introlab/OpenIMU-MiniLogger/Firmware-Arduino/src/imu.cpp

#include "imu.h"
#include "configmanager.h"
#include "sdcard.h"

IMU* IMU::_instance = NULL;

namespace
{
    /**
     * Interrupt handler will wake up the readIMU task at every sample (for each axis). 
     */
    void IRAM_ATTR imu_gpio_isr_handler(void* arg)
    {
        IMU *imu = (IMU*) (arg);
        assert(imu != NULL);
        xSemaphoreGiveFromISR(imu->getSemaphore(), NULL);
    }


    void readIMU(void *pvParameters)
    {
        printf("readIMU starting \n");
        IMU *imu = (IMU*) (pvParameters);
        assert(imu != NULL);

        TickType_t lastPrint = xTaskGetTickCount();
        TickType_t now;

        while(1)
        {
            xSemaphoreTake(imu->getSemaphore(), portMAX_DELAY);
            //printf("should read from task\n");
            imuDataPtr_t data = (imuDataPtr_t) malloc(sizeof(imuData_t));
            imu->readSensor(data);

            //Print at 4 Hz for debug
            /*
            now = xTaskGetTickCount();
            if (now - lastPrint > 250 / portTICK_RATE_MS)
            {
                printf("\nAccel : %.2f\t%.2f\t%.2f\n", data->accelX, data->accelY, data->accelZ);
                printf("Mag   : %.2f\t%.2f\t%.2f\n", data->magX, data->magY, data->magZ);
                printf("Gyro  : %.2f\t%.2f\t%.2f\n", data->gyroX, data->gyroY, data->gyroZ);
                lastPrint = now;
            }
            */

            //Send to queue, delete if not working
            if (!SDCard::instance()->enqueue(data))
                free(data);


        }
    }

}



IMU::IMU()
    : _mpu9250(), _readIMUHandle(NULL)
{
    if (_mpu9250.begin() == 0)
    {
        //IMUconfig_Sd SdConfig={100,500,8};

        setIMUParameter(ConfigManager::instance()->getIMUConfig());
               
        //SDCard::instance()->GetConfigFromSd(&SdConfig);
        //setIMUParameter(SdConfig.IMUSampleRate,SdConfig.IMUAcellRange,SdConfig.IMUGyroRange);

        printf("initialisation\n");


        // Enable FIFO
        //_mpu9250.enableFifo(true, true, true, true);

        
        // Setup interrupt handling
        _semaphore = xSemaphoreCreateCounting(1,0);
        setup_interrupt_pin();
        _mpu9250.enableInterrupt();
        _mpu9250.setIntLevel(INT_ACTIVE_LOW);

        //Create reading task, maximum priority
        xTaskCreatePinnedToCore(&readIMU, "IMU read task", 2048, this, configMAX_PRIORITIES -1, &_readIMUHandle, 0);
        //xTaskCreate(&readIMU, "IMU read task", 2048, this, 10, &_readIMUHandle);
        printf("IMU initialized\n");
    }
    else
    {
        printf("ERROR initializing IMU\n");
    }
}

void IMU::readSensor(imuDataPtr_t data)
{
    _mpu9250.update();

    if (data)
    {
        data->accelX = _mpu9250.calcAccel(_mpu9250.ax);
        data->accelY = _mpu9250.calcAccel(_mpu9250.ay);
        data->accelZ = _mpu9250.calcAccel(_mpu9250.az);
        data->gyroX  = _mpu9250.calcGyro(_mpu9250.gx);
        data->gyroY  = _mpu9250.calcGyro(_mpu9250.gy);
        data->gyroZ  = _mpu9250.calcGyro(_mpu9250.gz);
        data->magX = _mpu9250.calcMag(_mpu9250.mx);
        data->magY = _mpu9250.calcMag(_mpu9250.my);
        data->magZ = _mpu9250.calcMag(_mpu9250.mz);

    }
}

IMU* IMU::instance()
{
    if (IMU::_instance == NULL)
        IMU::_instance = new IMU();
    return IMU::_instance;
}

void IMU::setup_interrupt_pin()
{
    gpio_config_t io_conf;
    //interrupt on falling edge
    io_conf.intr_type = (gpio_int_type_t) GPIO_PIN_INTR_NEGEDGE;
    //set as input mode
    io_conf.mode = GPIO_MODE_INPUT;
    //bit mask of the pins that you want to set,e.g.GPIO33
    io_conf.pin_bit_mask =  (1ULL << INTERRUPT_PIN);
    //disable pull-down mode
    io_conf.pull_down_en = (gpio_pulldown_t) 0;
    //enable pull-up mode
    io_conf.pull_up_en = (gpio_pullup_t) 1;
    //configure GPIO with the given settings
    gpio_config(&io_conf);


    //Set ISR
    gpio_isr_handler_add((gpio_num_t)INTERRUPT_PIN, imu_gpio_isr_handler, this);
}

void IMU::setSampleRate(int rateHz)
{
    if (rateHz==10)
    {
        //_mpu9250.setDlpfBandwidth(DLPF_BANDWIDTH_5HZ);
        _mpu9250.setSampleRate(10);
        _mpu9250.setCompassSampleRate(10);

        printf("Set sample Rate:10Hz\n");
        SampleRateHz=10;
    }
    else if (rateHz==50)
    {
        //_mpu9250.setDlpfBandwidth(DLPF_BANDWIDTH_5HZ);
        _mpu9250.setSampleRate(50);
        _mpu9250.setCompassSampleRate(50);
        
        printf("Set sample Rate:50Hz\n");

        SampleRateHz=50;
    }
    else if (rateHz==100)
    {
        //_mpu9250.setLPF(42);
        _mpu9250.setSampleRate(100);
        _mpu9250.setCompassSampleRate(100);
        
        printf("Set sample Rate:100Hz\n");

        SampleRateHz=100;
    }
    else if (rateHz==200)
    {
        //_mpu9250.setLPF(98);
        _mpu9250.setSampleRate(200);
        _mpu9250.setCompassSampleRate(100);
        
        printf("Set sample Rate:200Hz\n");

        SampleRateHz=200;
    }
    else
    {
        _mpu9250.setSampleRate(100);
        _mpu9250.setCompassSampleRate(100);
        printf("Wrong rate entered,setting to 100Hz");

        SampleRateHz=100;
    }
    
}

void IMU::setGyroRange(int Gyrorange)
{
    if (Gyrorange==250 || Gyrorange == 500 || Gyrorange == 1000 || Gyrorange == 2000)
    {
        _mpu9250.setGyroFSR(Gyrorange);
        printf("Set Gyroscope range: %d\n",Gyrorange);
        GyroRangeDPS=Gyrorange;
    }
    else 
    {
        printf("Wrong range entered, setting to 500 dps\n");
        _mpu9250.setGyroFSR(500);
    }
}

void IMU::setAccelRange(int Accelrange)
{
    if (Accelrange==2 || Accelrange == 4 || Accelrange == 8 || Accelrange == 16)
    {
        _mpu9250.setAccelFSR(Accelrange);
        printf("Set Accelerometer range: %d\n",Accelrange);
        AccelRangeG=Accelrange;
    }
    else 
    {
        printf("Wrong range entered, setting to 4 g\n");
        _mpu9250.setAccelFSR(4);
    }
}

void IMU::setIMUParameter(int rateHZ,int accelRange, int gyroRange)
{
    // The sample rate of the accel/gyro can be set using
    // setSampleRate. Acceptable values range from 4Hz to 1kHz

    setSampleRate(rateHZ);

    // Accel options are +/- 2, 4, 8, or 16 g
    setAccelRange(accelRange);
    
    // Use setGyroFSR() and setAccelFSR() to configure the
    // gyroscope and accelerometer full scale ranges.
    // Gyro options are +/- 250, 500, 1000, or 2000 dps
    setGyroRange(gyroRange);
  
}

void IMU::setIMUParameter(const IMUconfig_Sd &config)
{
    setIMUParameter(config.IMUSampleRate, config.IMUAcellRange, config.IMUGyroRange);
}

int IMU::getSampleRate()
{
    int id = 0;
    if (SampleRateHz==10)
        id = 1;
    else if (SampleRateHz==50)
        id = 2;
    else if (SampleRateHz==100)
        id = 3;
    else if (SampleRateHz==200)
        id = 4;

    return id;
}

int IMU::getGyroRange()
{
    int id = 0;
    if (GyroRangeDPS==250)
        id = 1;
    else if (GyroRangeDPS==500)
        id = 2;
    else if (GyroRangeDPS==1000)
        id = 3;
    else if (GyroRangeDPS==2000)
        id = 4;

    return id;
}

int IMU::getAccelRange()
{
    int id = 0;
    if (AccelRangeG==2)
        id = 1;
    else if (AccelRangeG==4)
        id = 2;
    else if (AccelRangeG==8)
        id = 3;
    else if (AccelRangeG==16)
        id = 4;

    return id;
}


int IMU::getStepCount()
{
    return _mpu9250.dmpGetPedometerSteps();
}
    
int IMU::getStepTime()
{
    return _mpu9250.dmpGetPedometerTime()/1000;
}
