introlab/OpenIMU-MiniLogger/Firmware-Arduino/src/widget/icons.h

/*
 * Homescreen icons for Open Imu
 * 
 * Export as 1bpp in GIMP
 * Convert with https://littlevgl.com/image-to-c-array
 * 
 * author: Cedric Godin
 * 
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
 * THE SOFTWARE IS PROVIDED "AS IS", WITHOUT WARRANTY OF ANY KIND, EXPRESS OR IMPLIED, INCLUDING BUT NOT
 * LIMITED TO THE WARRANTIES OF MERCHANTABILITY, FITNESS FOR A PARTICULAR PURPOSE AND NONINFRINGEMENT.
 * IN NO EVENT SHALL THE AUTHORS OR COPYRIGHT HOLDERS BE LIABLE FOR ANY CLAIM, DAMAGES OR OTHER LIABILITY,
 * WHETHER IN AN ACTION OF CONTRACT, TORT OR OTHERWISE, ARISING FROM, OUT OF OR IN CONNECTION WITH THE SOFTWARE
 * OR THE USE OR OTHER DEALINGS IN THE SOFTWARE.
 */

#pragma once

#define GPS_ICON_WIDTH 13
#define GPS_ICON_HEIGHT 26

const unsigned char gps_icon[] = {
  0x0f, 0x80, 
  0x30, 0x60, 
  0x60, 0x30, 
  0x4f, 0x90, 
  0x90, 0x48, 
  0x90, 0x48, 
  0x90, 0x48, 
  0x90, 0x48, 
  0x90, 0x48, 
  0x4d, 0x90, 
  0x42, 0x10, 
  0x40, 0x10, 
  0x20, 0x10, 
  0x20, 0x20, 
  0x30, 0x20, 
  0x10, 0x40, 
  0x10, 0x40, 
  0x08, 0x80, 
  0x0c, 0x80, 
  0x05, 0x80, 
  0x37, 0x60, 
  0x43, 0x10, 
  0x82, 0x08, 
  0x80, 0x08, 
  0x60, 0x30, 
  0x1f, 0xc0
};

#define BATTERY_ICON_WIDTH 10
#define BATTERY_ICON_HEIGHT 25

const unsigned char battery_icon[] = {
  0x3f, 0x00, 
  0x21, 0x00, 
  0xff, 0xc0, 
  0x80, 0x40, 
  0x80, 0x40, 
  0x80, 0x40, 
  0x80, 0x40, 
  0x80, 0x40, 
  0x80, 0x40, 
  0x80, 0x40, 
  0x80, 0x40, 
  0x80, 0x40, 
  0x80, 0x40, 
  0x80, 0x40, 
  0x80, 0x40, 
  0x80, 0x40, 
  0x80, 0x40, 
  0x80, 0x40, 
  0x80, 0x40, 
  0x80, 0x40, 
  0x80, 0x40, 
  0x80, 0x40, 
  0x80, 0x40, 
  0x80, 0x40, 
  0xff, 0xc0
};

#define LOGGING_ICON_WIDTH 18
#define LOGGING_ICON_HEIGHT 21

const unsigned char logging_icon[] {
  0x00, 0x70, 0x00, 
  0x00, 0x50, 0x00, 
  0x00, 0x50, 0x00, 
  0x00, 0x50, 0x00, 
  0x01, 0xdc, 0x00, 
  0x01, 0x04, 0x00, 
  0x00, 0x88, 0x00, 
  0x00, 0x88, 0x00, 
  0x00, 0x50, 0x00, 
  0x1f, 0x77, 0xc0, 
  0x10, 0x20, 0x40, 
  0xff, 0xfe, 0x40, 
  0x80, 0x01, 0x40, 
  0x80, 0x01, 0x40, 
  0x40, 0x01, 0x40, 
  0x40, 0x01, 0xc0, 
  0x40, 0x00, 0xc0, 
  0x20, 0x00, 0xc0, 
  0x20, 0x00, 0xc0, 
  0x20, 0x00, 0x40, 
  0x3f, 0xff, 0xc0
};

#define SD_ICON_WIDTH 18
#define SD_ICON_HEIGHT 24

const unsigned char sd_icon[] {
  0x0f, 0xff, 0xc0, 
  0x10, 0x00, 0x40, 
  0x10, 0x00, 0x40, 
  0x20, 0x00, 0x40, 
  0x40, 0x00, 0x40, 
  0xc0, 0x00, 0x40, 
  0x80, 0x00, 0x40, 
  0x80, 0x00, 0x40, 
  0x80, 0x00, 0x40, 
  0x80, 0x00, 0x40, 
  0x80, 0x00, 0x40, 
  0x80, 0x00, 0x40, 
  0x9e, 0x78, 0x40, 
  0xb1, 0x46, 0x40, 
  0xa0, 0x43, 0x40, 
  0xa0, 0x41, 0x40, 
  0x9e, 0x41, 0x40, 
  0x83, 0x41, 0x40, 
  0x81, 0x41, 0x40, 
  0x81, 0x42, 0x40, 
  0xbe, 0x7c, 0x40, 
  0x80, 0x00, 0x40, 
  0x80, 0x00, 0x40, 
  0xff, 0xff, 0xc0
};

#define USB_ICON_WIDTH 15
#define USB_ICON_HEIGHT 25

const unsigned char usb_icon[] {
  0x01, 0x00, 
  0x01, 0x00, 
  0x03, 0x80, 
  0x03, 0x80, 
  0x07, 0xc0, 
  0x01, 0x00, 
  0x01, 0x00, 
  0x01, 0x1e, 
  0x01, 0x1e, 
  0x61, 0x1e, 
  0xf1, 0x1e, 
  0xf1, 0x04, 
  0x61, 0x0c, 
  0x41, 0x18, 
  0x61, 0xf0, 
  0x31, 0x00, 
  0x1d, 0x00, 
  0x03, 0x00, 
  0x01, 0x00, 
  0x01, 0x00, 
  0x03, 0x80, 
  0x07, 0xc0, 
  0x07, 0xc0, 
  0x07, 0xc0, 
  0x03, 0x80
};

#define SAMPLERATE_ICON_WIDTH 20
#define SAMPLERATE_ICON_HEIGHT 25

const unsigned char samplerate_icon[] = {
 0x00,0x00,0xf0,0x00,0x00,0xf0,0x06,0xfb,0xf7,0x06,0xfb,0xf7,
 0x06,0x03,0xf6,0x06,0x03,0xf6,0x06,0x03,0xf7,0x06,0x83,0xf3,
 0x06,0x83,0xf1,0x06,0x83,0xf1,0x06,0x83,0xf1,0xfe,0xc3,0xf0,
 0xfe,0xc3,0xf0,0x06,0xe3,0xf0,0x06,0x63,0xf0,0x06,0x63,0xf0,
 0x06,0x33,0xf0,0x06,0x3b,0xf0,0x06,0x1b,0xf0,0x06,0x1b,0xf0,
 0x06,0xfb,0xf7,0x06,0xfb,0xf7,0x00,0x00,0xf0,0x00,0x00,0xf0,
 0x00,0x00,0xf0};
