introlab/OpenIMU-MiniLogger/tests/OLED-Test-Firmware/include/ssd1331.h

/*****************************************************************************
*
* File                : ssd1331.h
* Hardware Environment: Raspberry Pi
* Build Environment   : GCC
* Version             : V1.0.7
* Author              : Yehui
*
*              (c) Copyright 2005-2017, WaveShare
*                   http://www.waveshare.com
*                   http://www.waveshare.net   
*                      All Rights Reserved
*              
******************************************************************************/

#ifndef _SSD1331_H_
#define _SSD1331_H_

//Display defines
#define OLED_WIDTH 96
#define OLED_HEIGHT 64

#define RGB(R,G,B)  (((R >> 3) << 11) | ((G >> 2) << 5) | (B >> 3))
enum Color {
    BLACK     = RGB(  0,  0,  0), // black
    GRAY      = RGB(192,192,192), // gray
    WHITE     = RGB(255,255,255), // white
    RED       = RGB(255,  0,  0), // red
    PINK      = RGB(255,192,203), // pink
    YELLOW    = RGB(255,255,  0), // yellow
    GOLDEN    = RGB(255,215,  0), // golden
    BROWN     = RGB(128, 42, 42), // brown
    BLUE      = RGB(  0,  0,255), // blue
    CYAN      = RGB(  0,255,255), // cyan
    GREEN     = RGB(  0,255,  0), // green
    PURPLE    = RGB(160, 32,240), // purple
};

enum ColorCMD {
    BLACK_CMD,
    GRAY_CMD,
    WHITE_CMD,
    RED_CMD,
    PINK_CMD,
    YELLOW_CMD,
    GOLDEN_CMD,
    BROWN_CMD,
    BLUE_CMD,
    CYAN_CMD,
    GREEN_CMD,
    PURPLE_CMD,
};

static const unsigned char color_cmd[12][3] =  {
    {0, 0, 0},
    {192, 192, 192},
    {255, 255, 255},
    {255,  0,  0},
    {255,192,203},
    {255,255,  0},
    {255,215,  0},
    {128, 42, 42},
    {  0,  0,255},
    {  0,255,255},
    {  0,255,  0},
    {160, 32,240},
};

#define DRAW_LINE                       0x21
#define DRAW_RECTANGLE                  0x22
#define COPY_WINDOW                     0x23
#define DIM_WINDOW                      0x24
#define CLEAR_WINDOW                    0x25
#define FILL_WINDOW                     0x26
#define DISABLE_FILL                    0x00
#define ENABLE_FILL                     0x01
#define CONTINUOUS_SCROLLING_SETUP      0x27
#define DEACTIVE_SCROLLING              0x2E
#define ACTIVE_SCROLLING                0x2F

#define SET_COLUMN_ADDRESS              0x15
#define SET_ROW_ADDRESS                 0x75
#define SET_CONTRAST_A                  0x81
#define SET_CONTRAST_B                  0x82
#define SET_CONTRAST_C                  0x83
#define MASTER_CURRENT_CONTROL          0x87
#define SET_PRECHARGE_SPEED_A           0x8A
#define SET_PRECHARGE_SPEED_B           0x8B
#define SET_PRECHARGE_SPEED_C           0x8C
#define SET_REMAP                       0xA0
#define SET_DISPLAY_START_LINE          0xA1
#define SET_DISPLAY_OFFSET              0xA2
#define NORMAL_DISPLAY                  0xA4
#define ENTIRE_DISPLAY_ON               0xA5
#define ENTIRE_DISPLAY_OFF              0xA6
#define INVERSE_DISPLAY                 0xA7
#define SET_MULTIPLEX_RATIO             0xA8
#define DIM_MODE_SETTING                0xAB
#define SET_MASTER_CONFIGURE            0xAD
#define DIM_MODE_DISPLAY_ON             0xAC
#define DISPLAY_OFF                     0xAE
#define NORMAL_BRIGHTNESS_DISPLAY_ON    0xAF
#define POWER_SAVE_MODE                 0xB0
#define PHASE_PERIOD_ADJUSTMENT         0xB1
#define DISPLAY_CLOCK_DIV               0xB3
#define SET_GRAy_SCALE_TABLE            0xB8
#define ENABLE_LINEAR_GRAY_SCALE_TABLE  0xB9
#define SET_PRECHARGE_VOLTAGE           0xBB

#define SET_V_VOLTAGE                   0xBE

void SSD1331_begin();
void SSD1331_display();
void SSD1331_clear();
void SSD1331_shutdown();
void SSD1331_pixel(int x,int y, char color);
void SSD1331_rectangle(int x1, int y1, int x2, int y2, unsigned short hwColor, bool filled = false);
void SSD1331_line(int x1, int y1, int x2, int y2, unsigned short hwColor);
void SSD1331_mono_bitmap(unsigned char x, unsigned char y, const unsigned char *pBmp, char chWidth, char chHeight, unsigned short hwColor);
void SSD1331_bitmap24(unsigned char x, unsigned char y, unsigned char *pBmp, char chWidth, char chHeight);
void SSD1331_string(unsigned char x, unsigned char y, const char *pString, unsigned char Size, unsigned char Mode, unsigned short hwColor);
void SSD1331_char1616(unsigned char x, unsigned char y, unsigned char chChar, unsigned short hwColor);
void SSD1331_char3216(unsigned char x, unsigned char y, unsigned char chChar, unsigned short hwColor);

void SSD1331_clear_screen(unsigned short hwColor);
void SSD1331_draw_point(int chXpos, int chYpos, unsigned short hwColor);

static const unsigned char waveshare_logo[1024]=
{/*0X00,0X01,0X60,0X00,0X40,0X00,*/
    0X00,0X00,0X00,0X00,0X00,0X00,0X00,0X00,0X00,0X00,0X00,0X00,0X00,0X00,0X00,0X00,
    0X00,0X00,0X00,0X00,0X00,0X00,0X00,0X00,0X00,0X00,0X00,0X00,0X00,0X00,0X00,0X00,
    0X00,0X00,0X00,0X00,0X00,0X00,0X00,0X00,0X00,0X00,0X00,0X00,0X00,0X00,0X00,0X00,
    0X41,0X83,0X0C,0X30,0X33,0XF1,0XF8,0XC1,0X81,0X81,0XFC,0X7E,0X61,0XC2,0X0E,0X10,
    0X33,0X03,0X00,0XC1,0X83,0X81,0X8C,0X60,0X61,0XC2,0X1A,0X18,0X23,0X03,0X00,0XC1,
    0X82,0XC1,0X84,0X60,0X63,0X46,0X12,0X18,0X63,0X03,0X00,0XC1,0X82,0X41,0X84,0X60,
    0X23,0X46,0X33,0X08,0X43,0X01,0X80,0XC1,0X86,0X61,0X8C,0X60,0X32,0X64,0X31,0X0C,
    0XC3,0XF0,0XE0,0XFF,0X84,0X61,0XF8,0X7E,0X32,0X64,0X21,0X8C,0XC3,0X00,0X30,0XC1,
    0X8C,0X21,0XF0,0X60,0X16,0X2C,0X7F,0X84,0X83,0X00,0X18,0XC1,0X8F,0XF1,0X98,0X60,
    0X1C,0X3C,0X7F,0X87,0X83,0X00,0X18,0XC1,0X8F,0XF1,0X8C,0X60,0X1C,0X38,0XC0,0XC7,
    0X83,0X02,0X18,0XC1,0X98,0X11,0X86,0X60,0X0C,0X18,0XC0,0XC3,0X03,0XF3,0XF0,0XC1,
    0X98,0X19,0X86,0X7E,0X08,0X18,0X80,0X43,0X03,0XF0,0XE0,0XC1,0X90,0X09,0X02,0X7E,
    0X00,0X00,0X00,0X00,0X00,0X00,0X00,0X00,0X00,0X00,0X00,0X00,0X00,0X00,0X00,0X00,
    0X00,0X00,0X00,0X00,0X00,0X00,0X00,0X00,0X00,0X00,0X00,0X00,0X00,0X00,0X00,0X00,
    0X00,0X00,0X00,0X00,0X00,0X00,0X00,0X00,0X00,0X00,0X00,0X00,0X00,0X00,0X00,0X00,
    0X00,0X00,0X00,0X00,0X00,0X00,0X00,0X00,0X00,0X00,0X00,0X00,0X00,0X00,0X00,0X00,
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
{
    0x18,0x54,0x32,0x1C,0x1C,0x32,0x54,0x18
};

static const unsigned char GPRS88[8] = //GPRS
{
    0xC3,0x99,0x24,0x20,0x2C,0x24,0x99,0xC3
};

static const unsigned char Alarm88[8] = //alram
{
    0xC3,0xBD,0x42,0x52,0x4E,0x42,0x3C,0xC3
};

#endif
